DianaAndreeaRaceu/Proiect_TSC/Images/c.png

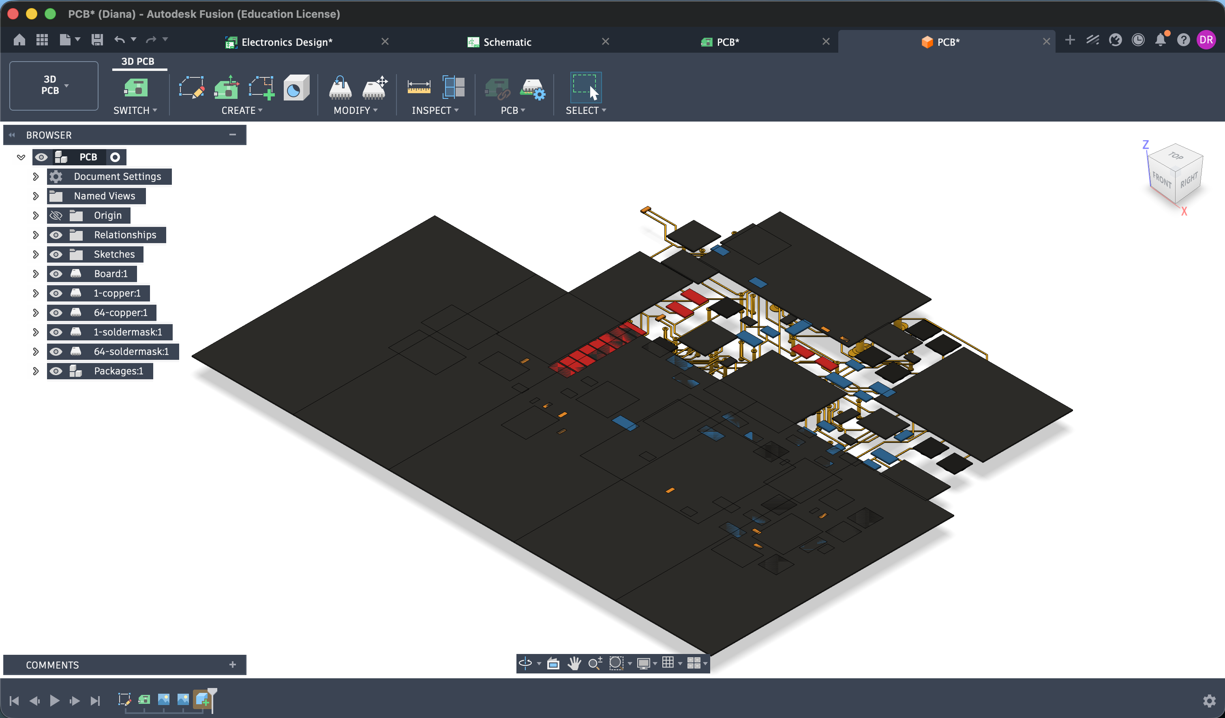
Images/c.png
