DianaAndreeaRaceu/Proiect_TSC/Images/pcb.png

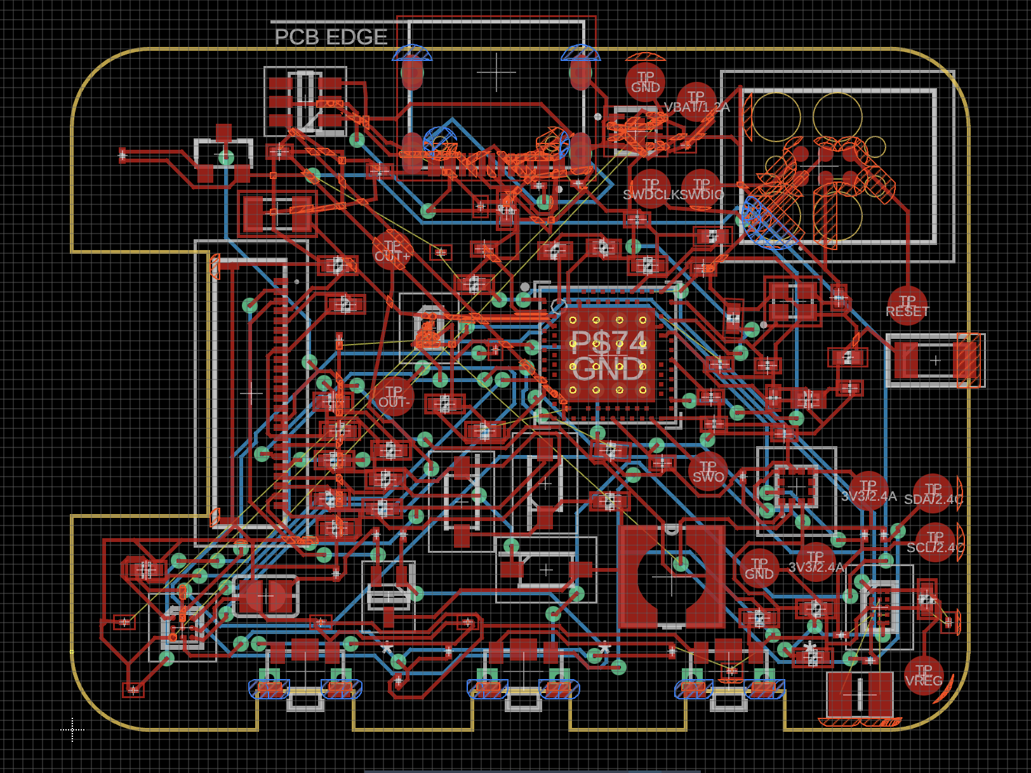
Images/pcb.png
