DianaAndreeaRaceu/Proiect_TSC/Images/s.png

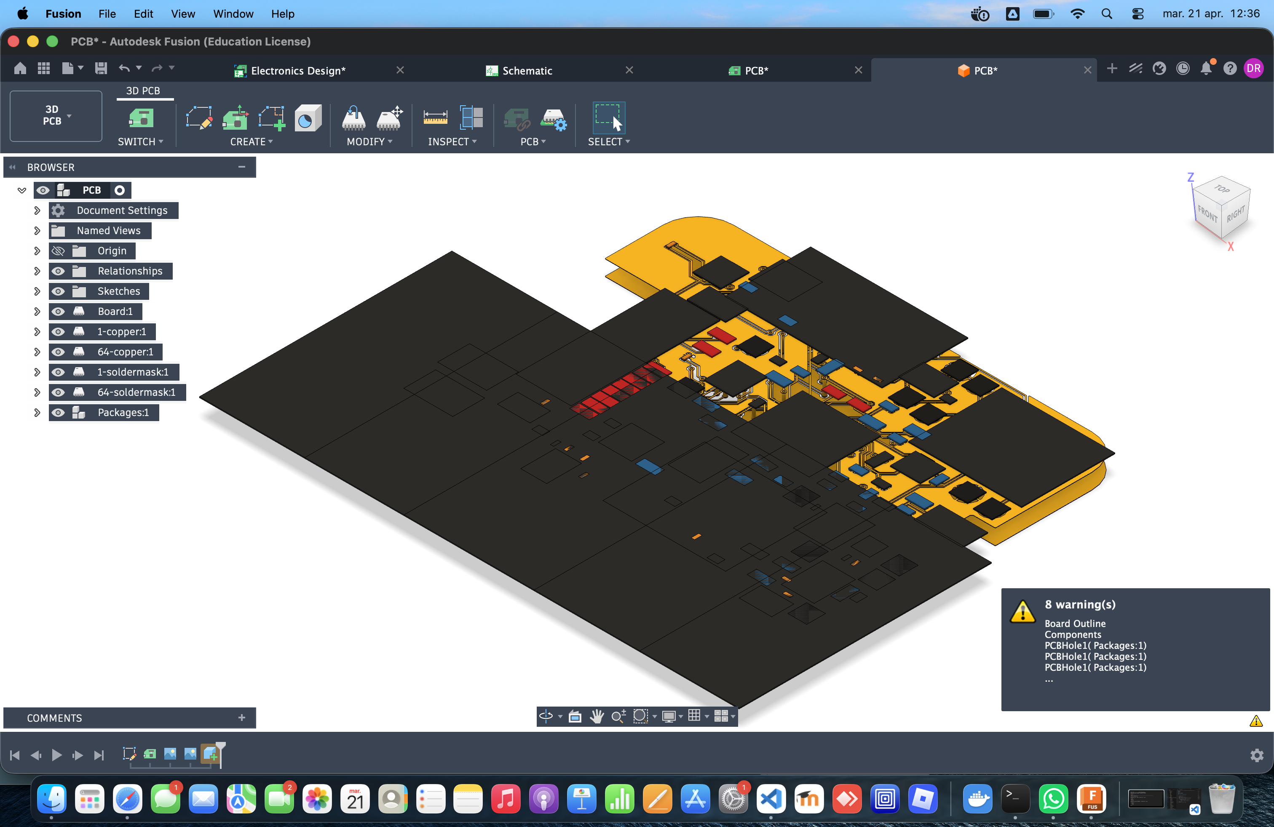
Images/s.png
